eduardoit/Project_weather_station/hardware/3d_models/pluviometro/rejilla.stl

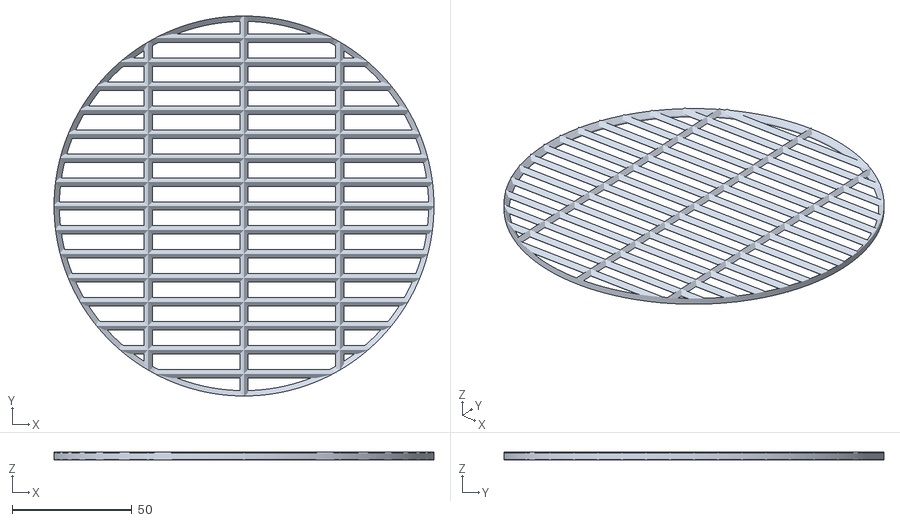
[picture p22: CAD file, 2025-10-21]
hardware/3d_models/pluviometro/rejilla.stl
158.5 x 158.5 x 3.18
