eduardoit/Project_weather_station/hardware/3d_models/RadiacionSolar_THP/SHT15_sensor_V1.stl

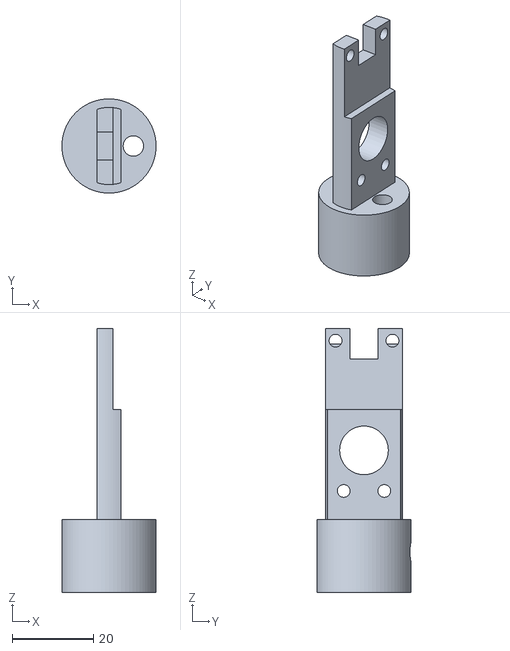
[picture p23: CAD file, 2025-10-21]
hardware/3d_models/RadiacionSolar_THP/SHT15_sensor_V1.stl
23.2 x 23.2 x 65.0
