eduardoit/Project_weather_station/hardware/3d_models/RadiacionSolar_THP/Rad_Shd_Top_V1.stl

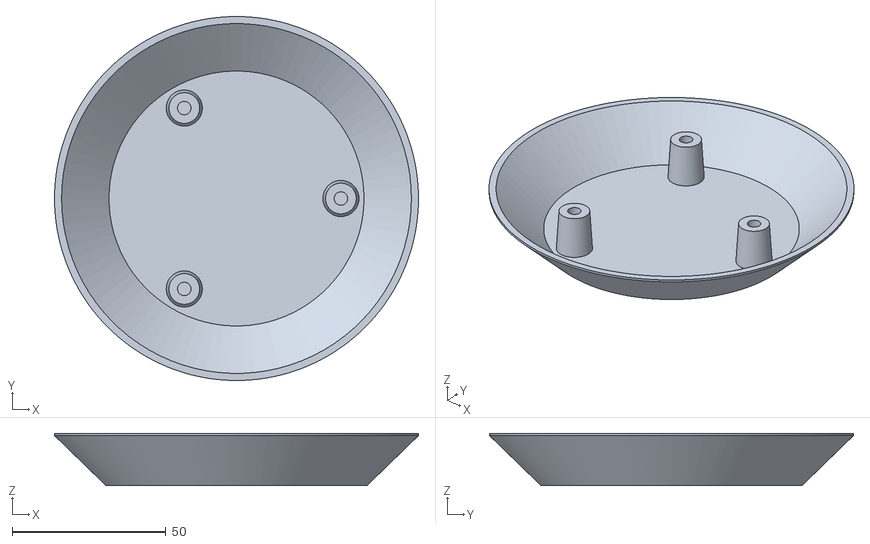
[picture p24: CAD file, 2025-10-21]
hardware/3d_models/RadiacionSolar_THP/Rad_Shd_Top_V1.stl
118.5 x 118.5 x 17.0
