eduardoit/Project_weather_station/hardware/3d_models/RadiacionSolar_THP/Rad_Shd_Horz_mount_V1.stl

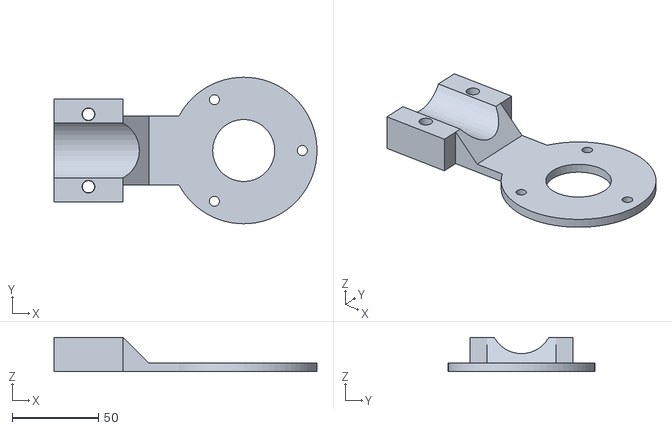
[picture p25: CAD file, 2025-10-21]
hardware/3d_models/RadiacionSolar_THP/Rad_Shd_Horz_mount_V1.stl
152.5 x 85.0 x 20.0
