eduardoit/Project_weather_station/hardware/3d_models/pluviometro/img/montajePluviometro.jpg

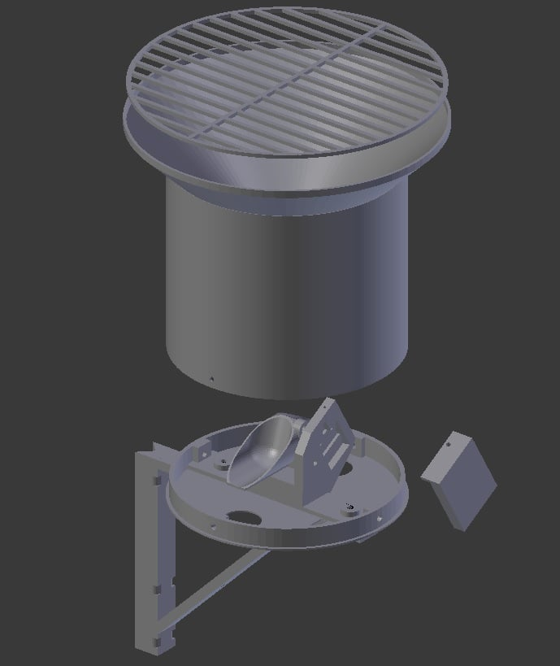
hardware/3d_models/pluviometro/img/montajePluviometro.jpg
